TheSaturdayThing/laser_seal_arduino/laser_cutter_files/MIT_Crest_Vectorized.dxf

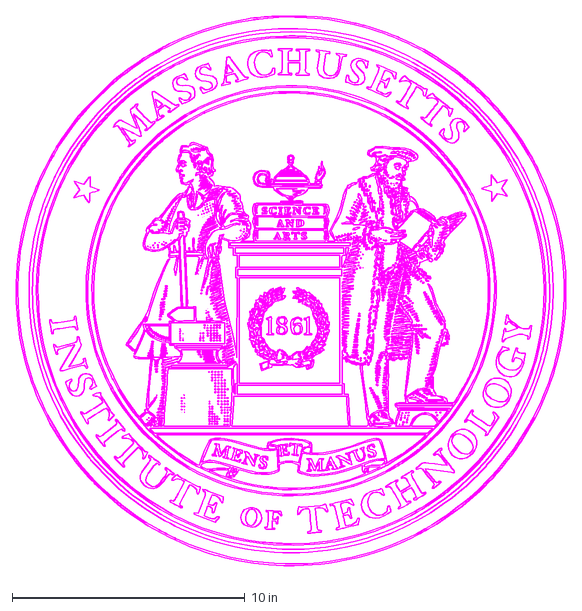
[picture p15: CAD file, 2025-09-28]
laser_cutter_files/MIT_Crest_Vectorized.dxf
23.6 x 23.9 in
