TheSaturdayThing/laser_seal_arduino/laser_cutter_files/laser harp with vines sheet two.dxf

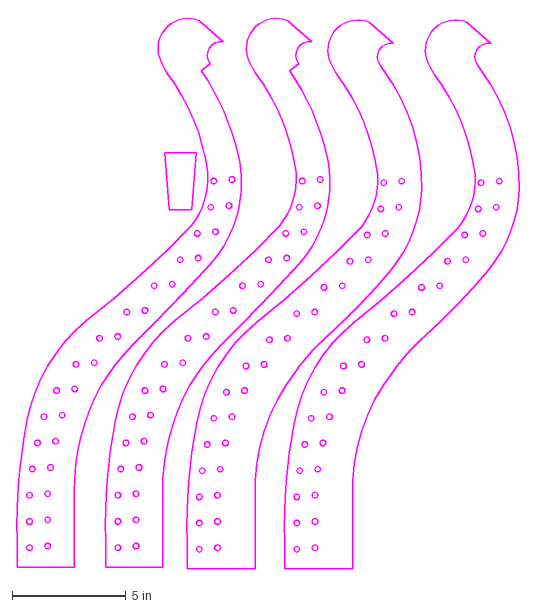
[picture p16: CAD file, 2025-09-28]
laser_cutter_files/laser harp with vines sheet two.dxf
22.1 x 24.3 in
