TheSaturdayThing/laser_seal_arduino/laser_cutter_files/laser circle 28 inch sheet one.dxf

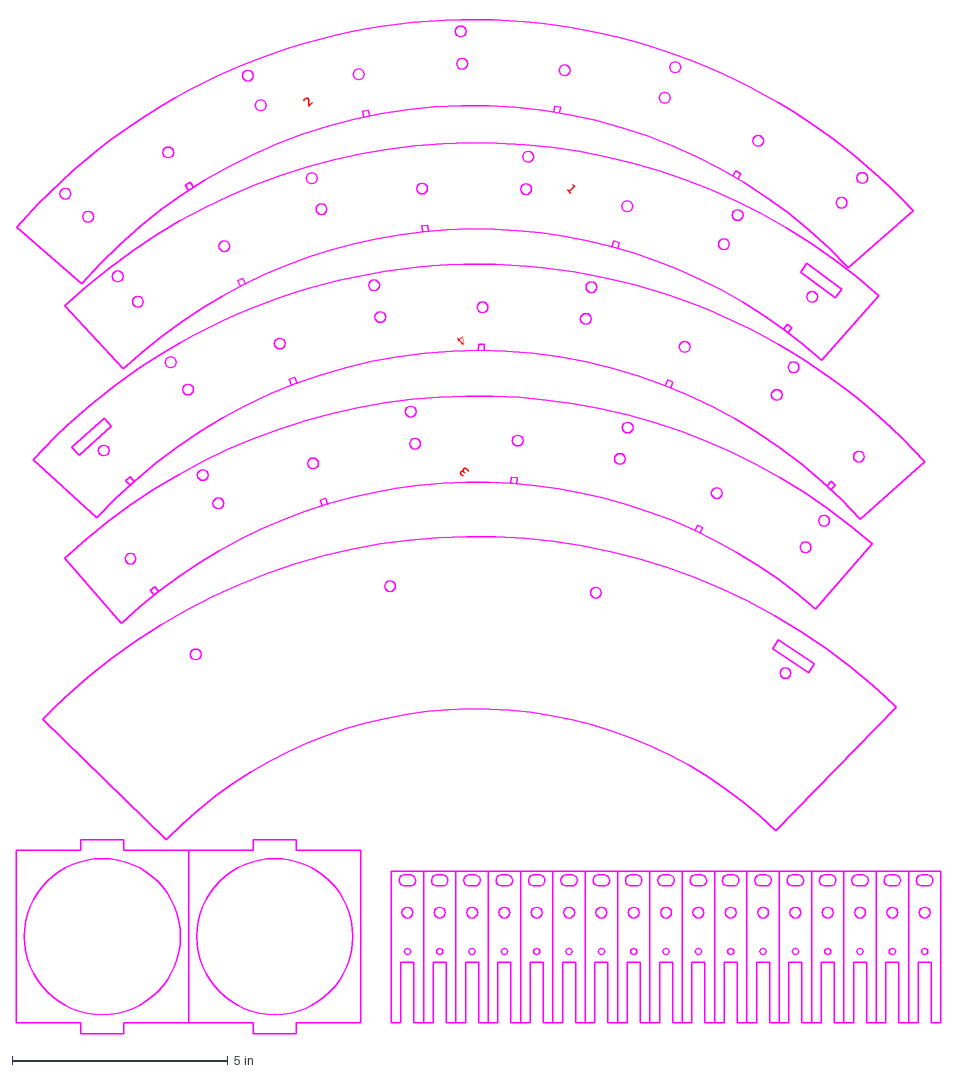
[picture p17: CAD file, 2025-09-28]
laser_cutter_files/laser circle 28 inch sheet one.dxf
1
2
3
4
