TheSaturdayThing/laser_seal_arduino/laser_cutter_files/laser circle safe vesion sheet two.dxf

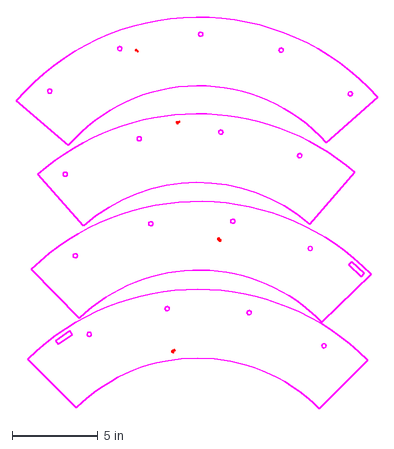
[picture p18: CAD file, 2025-09-28]
laser_cutter_files/laser circle safe vesion sheet two.dxf
21.0 x 22.8 in
