TheSaturdayThing/laser_seal_arduino/laser_cutter_files/laser harp 28 inch center circle.dxf

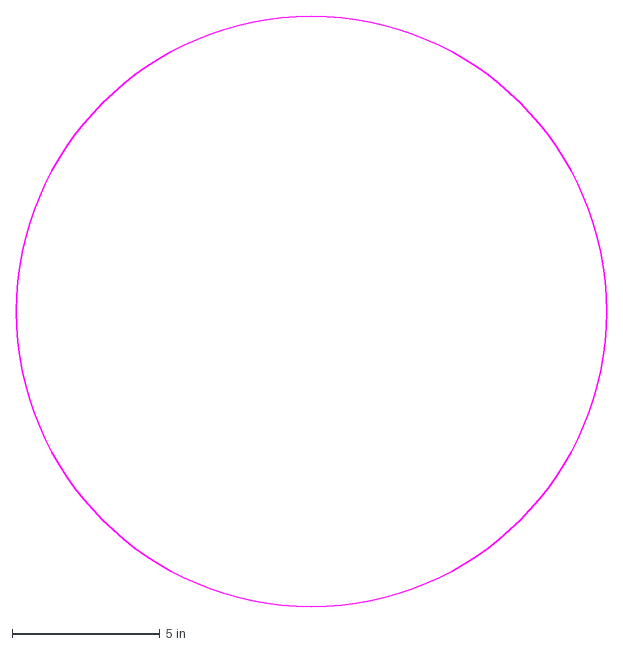
[picture p19: CAD file, 2025-09-28]
laser_cutter_files/laser harp 28 inch center circle.dxf
20.0 x 20.0 in
