TheSaturdayThing/laser_seal_arduino/laser_cutter_files/laser circle sheet 1.dxf

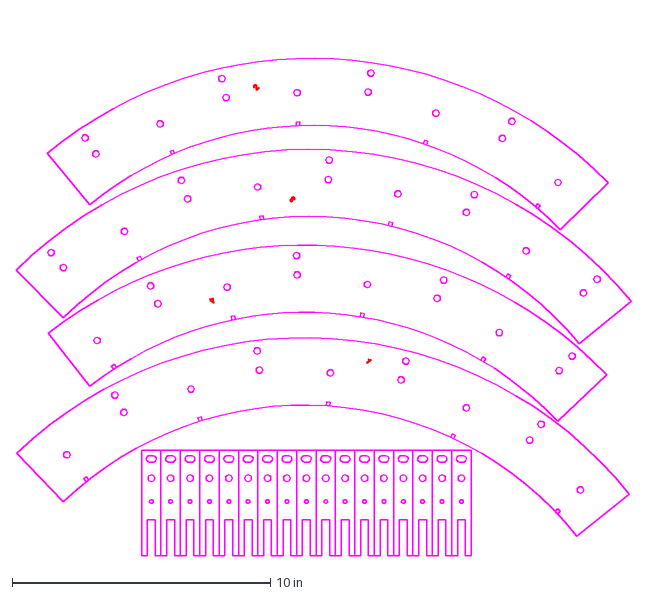
[picture p20: CAD file, 2025-09-28]
laser_cutter_files/laser circle sheet 1.dxf
23.8 x 20.9 in
