TheSaturdayThing/laser_seal_arduino/laser_cutter_files/laser circle safe version sheet one.dxf

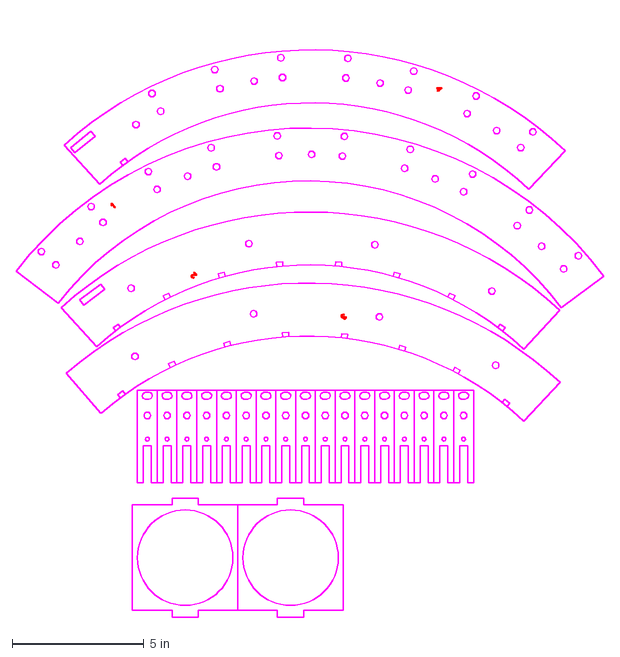
[picture p21: CAD file, 2025-09-28]
laser_cutter_files/laser circle safe version sheet one.dxf
22.3 x 22.8 in
