TheSaturdayThing/laser_seal_arduino/laser_cutter_files/laser circle seal center.dxf

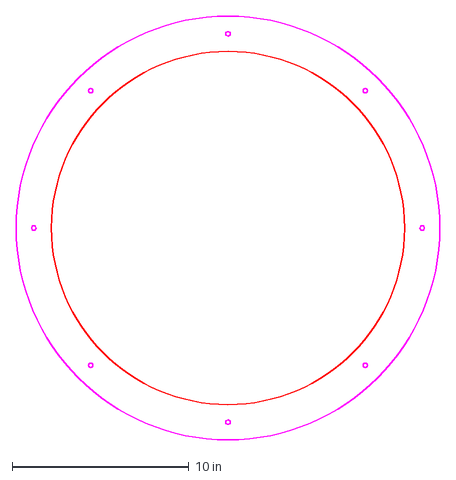
[picture p22: CAD file, 2025-09-28]
laser_cutter_files/laser circle seal center.dxf
24.0 x 24.0 in
