TheSaturdayThing/laser_seal_arduino/laser_cutter_files/laser harp 3 with vines sheet one.dxf

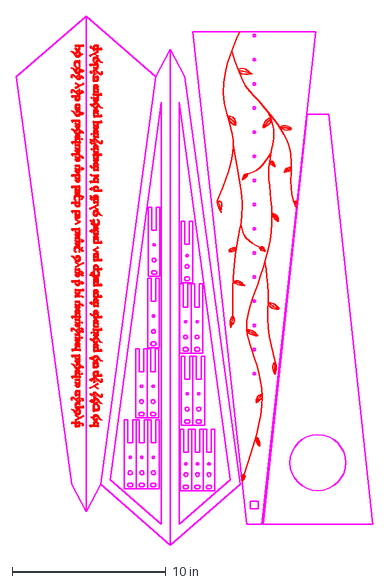
[picture p23: CAD file, 2025-09-28]
laser_cutter_files/laser harp 3 with vines sheet one.dxf
23.1 x 34.4 in
