TheSaturdayThing/laser_seal_arduino/laser_cutter_files/laser harp 3 sheet 2.dxf

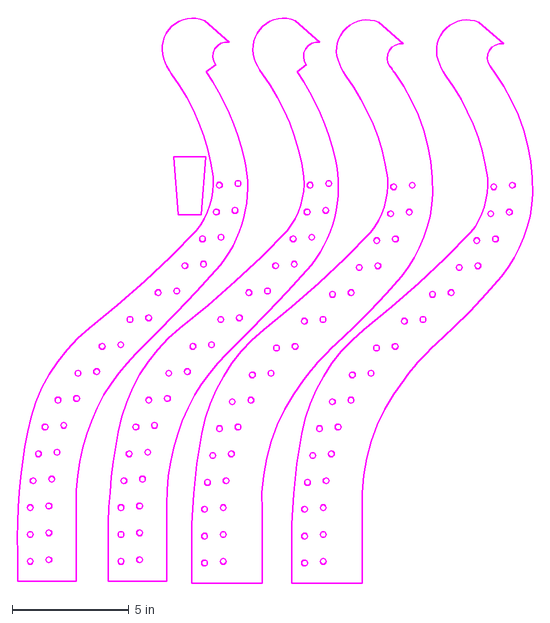
[picture p24: CAD file, 2025-09-28]
laser_cutter_files/laser harp 3 sheet 2.dxf
22.1 x 24.3 in
